wenbakefield/bent-wavefield/apc_synth/apc_synth.kicad_sch

## KiCad design apc_synth/apc_synth.kicad_sch (2023-07-06)

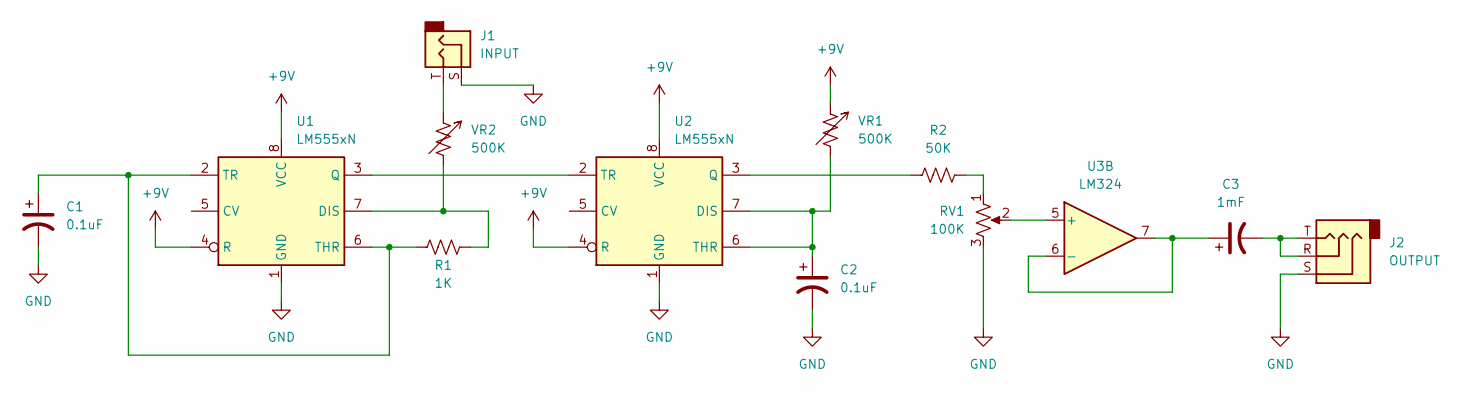
[picture p5: schematic apc_synth.kicad_sch]

Parts:
C1, C2: 0.1uF
C3: 1mF
J1: INPUT
J2: OUTPUT
R1: 1K
R2: 50K
RV1: 100K
U1, U2: LM555xN; DIP-8_W7.62mm
U3: LM324
VR1, VR2: 500K

Connections:
unnamed: C1.1, R1.1, U1.2 (TR), U1.6 (THR)
unnamed: C2.1, U2.6 (THR), U2.7 (DIS), VR1.2
unnamed: C3.1, U3.6 (-), U3.7
unnamed: C3.2, J2.R, J2.T
unnamed: J1.T, VR2.1
unnamed: R1.2, U1.7 (DIS), VR2.2
unnamed: R2.1, RV1.1
unnamed: R2.2, U2.3 (Q)
unnamed: RV1.2, U3.5 (+)
unnamed: U1.3 (Q), U2.2 (TR)
