wenbakefield/bent-wavefield/baby8_sequencer/baby8_sequencer.kicad_sch

## KiCad design baby8_sequencer/baby8_sequencer.kicad_sch (2023-07-06)

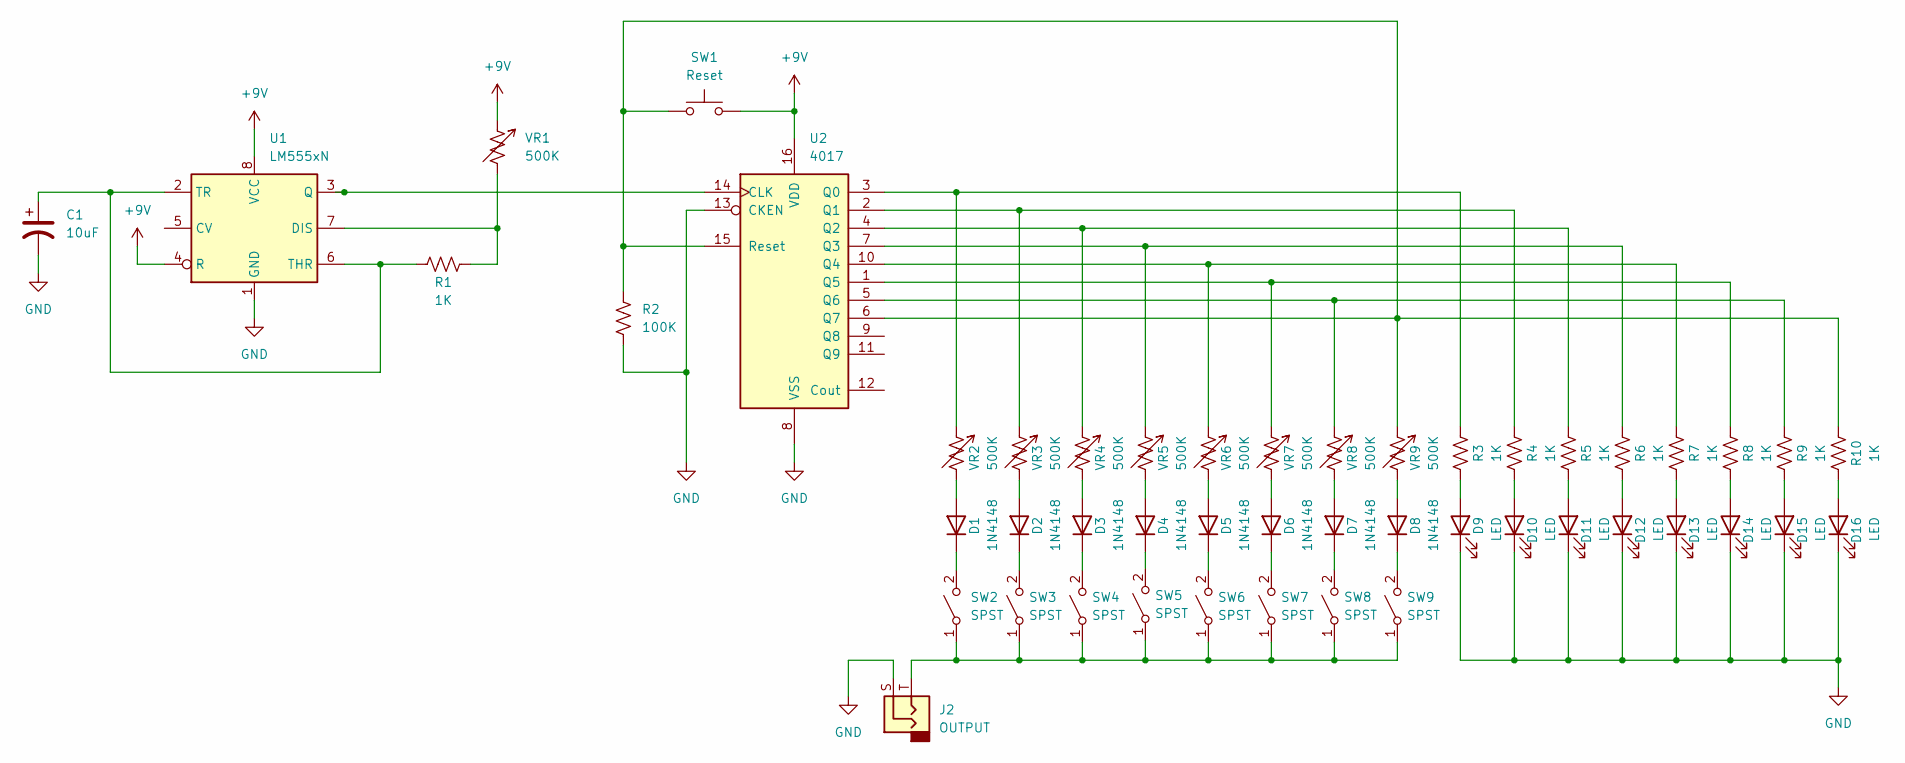
[picture p6: schematic baby8_sequencer.kicad_sch]

Parts:
C1: 10uF
D1, D2, D3, D4, D5, D6, D7, D8: 1N4148; D_DO-35_SOD27_P7.62mm_Horizontal
D9, D10, D11, D12, D13, D14, D15, D16: LED
J2: OUTPUT
R1, R3, R4, R5, R6, R7, R8, R9, R10: 1K
R2: 100K
SW1: Reset
SW2, SW3, SW4, SW5, SW6, SW7, SW8, SW9: SPST
U1: LM555xN; DIP-8_W7.62mm
U2: 4017
VR1, VR2, VR3, VR4, VR5, VR6, VR7, VR8, VR9: 500K

Connections:
+9V: SW1.2, U1.4 (R), U1.8 (VCC), U2.16 (VDD), VR1.1
GND: C1.2, D9.1 (K), D10.1 (K), D11.1 (K), D12.1 (K), D13.1 (K), D14.1 (K), D15.1 (K), D16.1 (K), J2.S, R2.2, U1.1 (GND), U2.8 (VSS), U2.13 (CKEN)
unnamed: C1.1, R1.2, U1.2 (TR), U1.6 (THR)
unnamed: D1.1 (K), SW2.2 (B)
unnamed: D1.2 (A), VR2.2
unnamed: D2.1 (K), SW3.2 (B)
unnamed: D2.2 (A), VR3.2
unnamed: D3.1 (K), SW4.2 (B)
unnamed: D3.2 (A), VR4.2
unnamed: D4.1 (K), SW5.2 (B)
unnamed: D4.2 (A), VR5.2
unnamed: D5.1 (K), SW6.2 (B)
unnamed: D5.2 (A), VR6.2
unnamed: D6.1 (K), SW7.2 (B)
unnamed: D6.2 (A), VR7.2
unnamed: D7.1 (K), SW8.2 (B)
unnamed: D7.2 (A), VR8.2
unnamed: D8.1 (K), SW9.2 (B)
unnamed: D8.2 (A), VR9.2
unnamed: D9.2 (A), R3.2
unnamed: D10.2 (A), R4.2
unnamed: D11.2 (A), R5.2
unnamed: D12.2 (A), R6.2
unnamed: D13.2 (A), R7.2
unnamed: D14.2 (A), R8.2
unnamed: D15.2 (A), R9.2
unnamed: D16.2 (A), R10.2
unnamed: J2.T, SW2.1 (A), SW3.1 (A), SW4.1 (A), SW5.1 (A), SW6.1 (A), SW7.1 (A), SW8.1 (A), SW9.1 (A)
unnamed: R1.1, U1.7 (DIS), VR1.2
unnamed: R3.1, U2.3 (Q0), VR2.1
unnamed: R4.1, U2.2 (Q1), VR3.1
unnamed: R5.1, U2.4 (Q2), VR4.1
unnamed: R6.1, U2.7 (Q3), VR5.1
unnamed: R7.1, U2.10 (Q4), VR6.1
unnamed: R8.1, U2.1 (Q5), VR7.1
unnamed: R9.1, U2.5 (Q6), VR8.1
unnamed: R2.1, R10.1, SW1.1, U2.6 (Q7), U2.15 (Reset), VR9.1
unnamed: U1.3 (Q), U2.14 (CLK)
